TypJag/VolumeMixer/Dokumentation/Bilder/20230328_190127.jpg

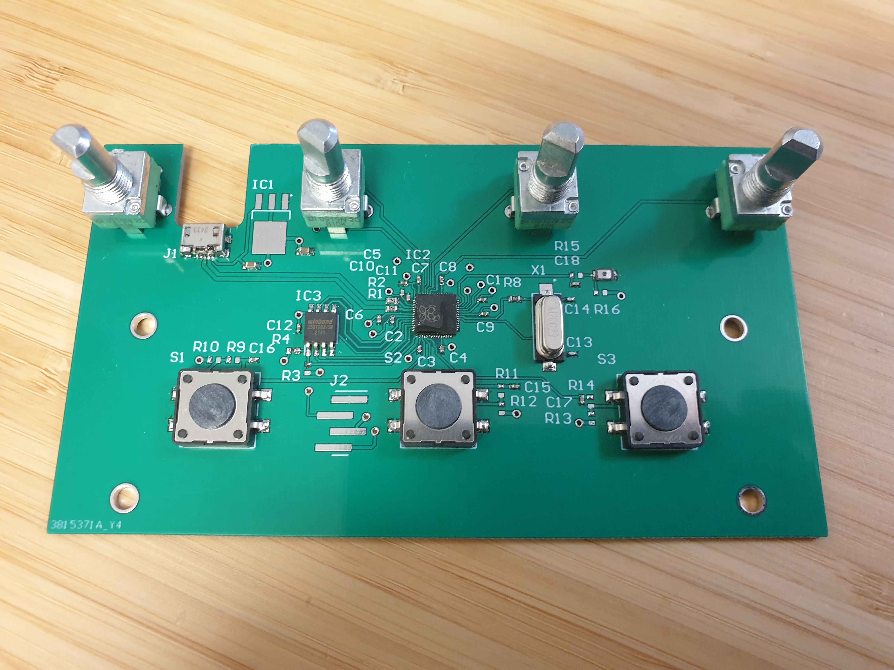
Dokumentation/Bilder/20230328_190127.jpg
