TypJag/VolumeMixer/Dokumentation/Bilder/IMG_0465.JPEG

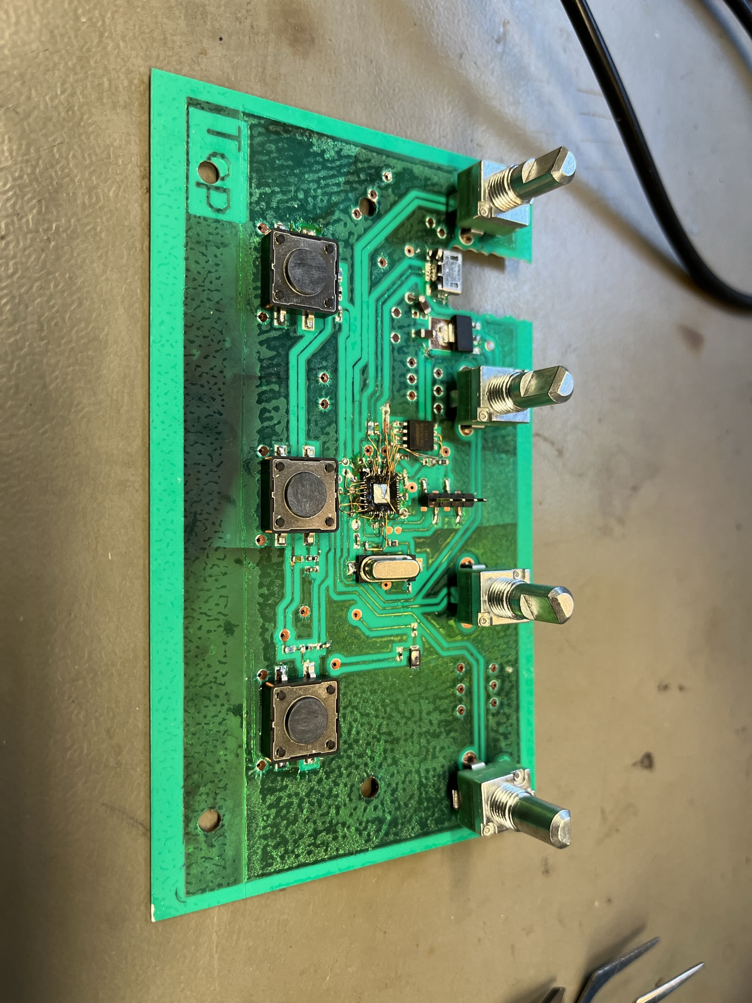
Dokumentation/Bilder/IMG_0465.JPEG
