TypJag/VolumeMixer/CAD/Knapp alt.SLDPRT

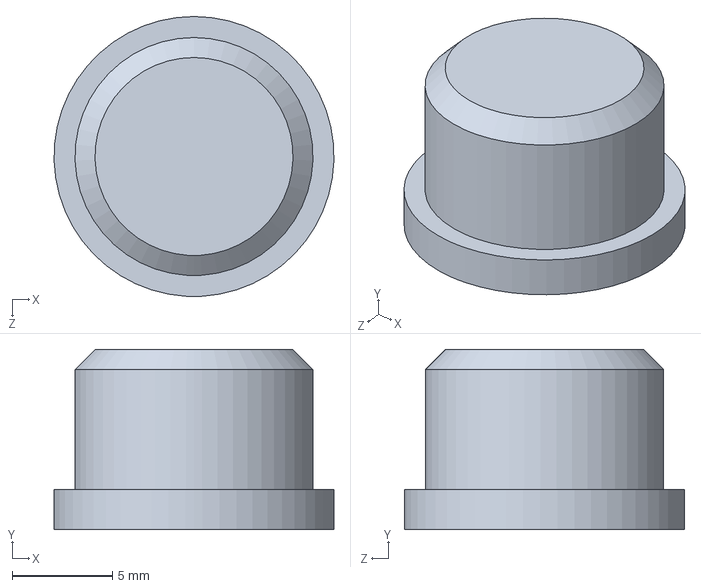
[picture p45: CAD file, 2023-03-03]
CAD/Knapp alt.SLDPRT
14.0 x 9.00 x 14.0 mm
