TypJag/VolumeMixer/CAD/Spacer small.SLDPRT

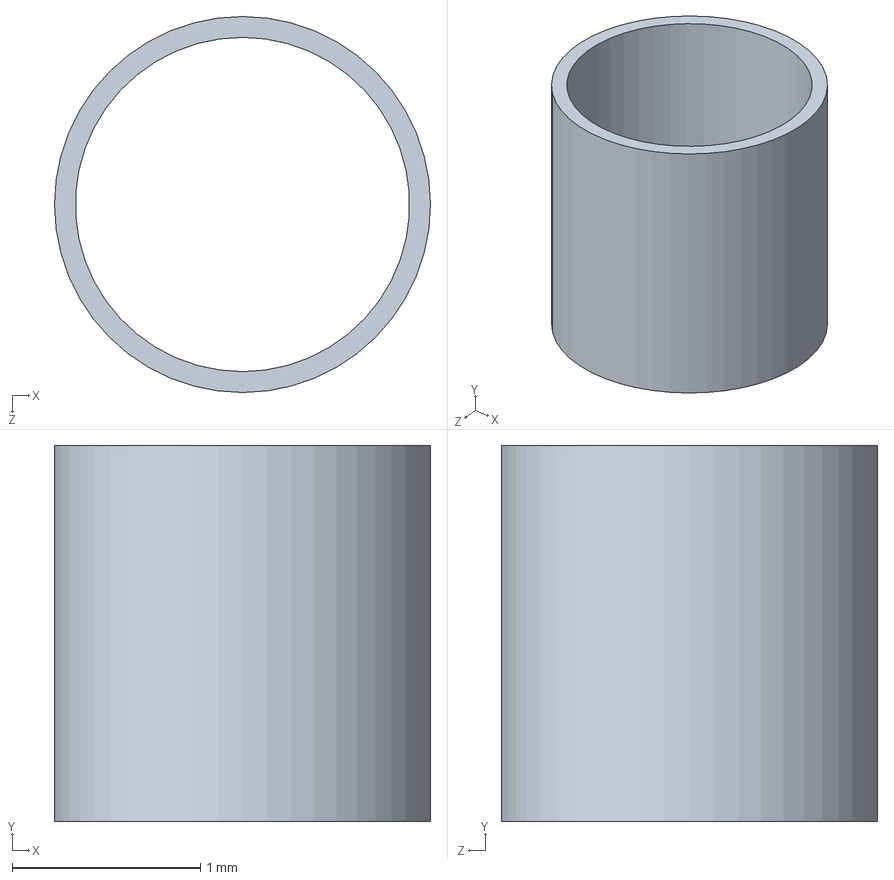
[picture p46: CAD file, 2023-03-03]
CAD/Spacer small.SLDPRT
2.00 x 2.00 x 2.00 mm
