TypJag/VolumeMixer/CAD/PCB.SLDPRT

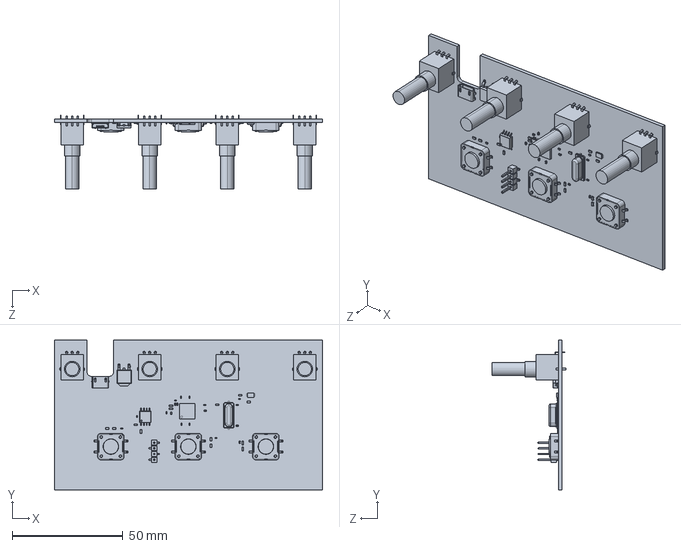
[picture p47: CAD file, 2023-03-03]
CAD/PCB.SLDPRT
121.0 x 67.5 x 33.5 mm
