TypJag/VolumeMixer/CAD/Keyplate 3mm.STL

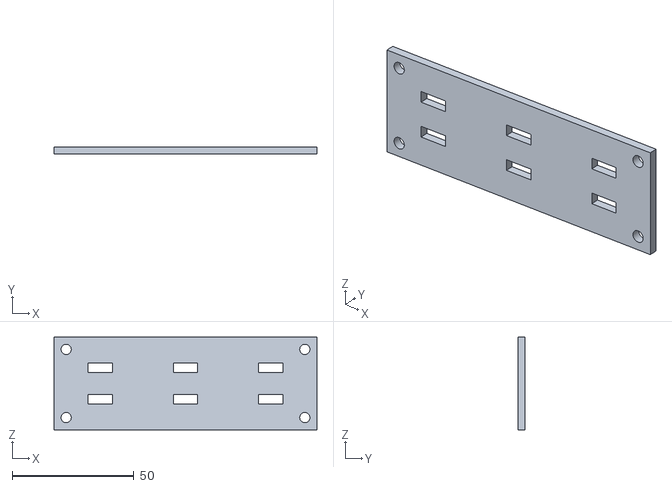
[picture p48: CAD file, 2023-03-03]
CAD/Keyplate 3mm.STL
108.0 x 3.00 x 38.0
