TypJag/VolumeMixer/CAD/Knapp.SLDPRT

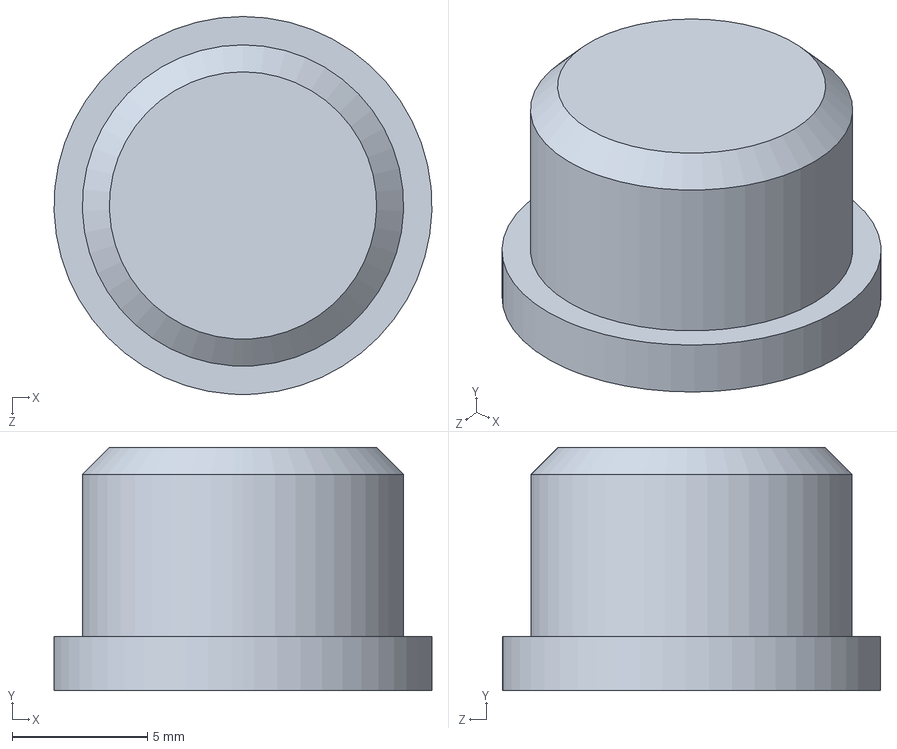
[picture p49: CAD file, 2023-03-03]
CAD/Knapp.SLDPRT
14.0 x 9.00 x 14.0 mm
