TypJag/VolumeMixer/CAD/Skrew M4 12mm.SLDPRT

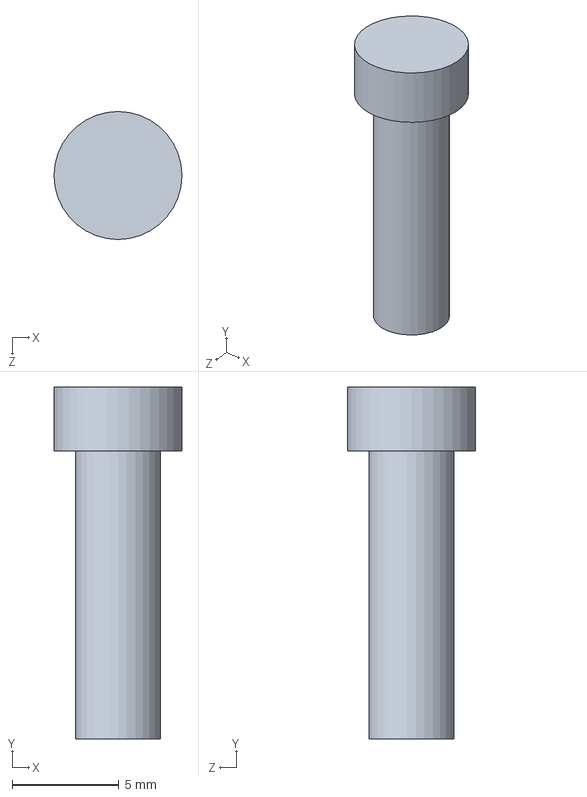
[picture p50: CAD file, 2023-03-03]
CAD/Skrew M4 12mm.SLDPRT
6.00 x 16.5 x 6.00 mm
