TypJag/VolumeMixer/CAD/Arduino Nano.SLDPRT

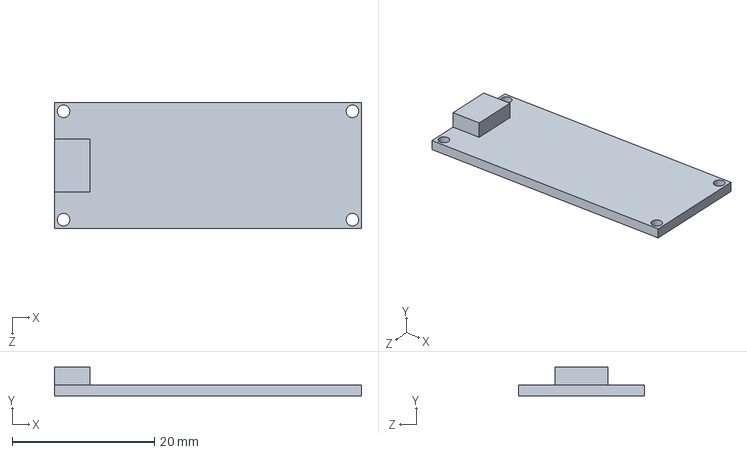
[picture p51: CAD file, 2023-03-03]
CAD/Arduino Nano.SLDPRT
43.2 x 4.07 x 17.8 mm
