TypJag/VolumeMixer/CAD/outline.SLDPRT

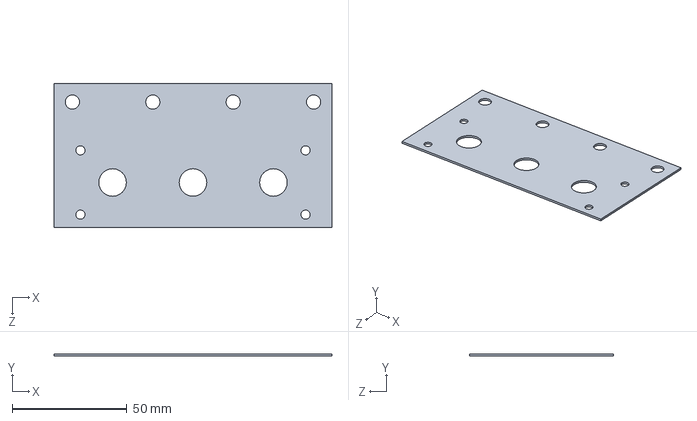
[picture p52: CAD file, 2023-03-03]
CAD/outline.SLDPRT
121.0 x 1.00 x 62.5 mm
